0kam/ShutterClock/docs/measurements/data/2026-10-07_d7500_run2_timeline_100ms.csv

t_s | mean_A | max_A | vmin_V
0.0 | 0.00042 | 0.0022 | 8.9875
0.1 | 0.00044 | 0.0019 | 8.9857
0.2 | 0.00042 | 0.0018 | 8.9838
0.3 | 0.00049 | 0.0020 | 8.9875
0.4 | 0.00044 | 0.0026 | 8.9875
0.5 | 0.00042 | 0.0019 | 8.9838
0.6 | 0.00043 | 0.0018 | 8.9885
0.7 | 0.00044 | 0.0022 | 8.9838
0.8 | 0.00039 | 0.0022 | 8.9818
0.9 | 0.00044 | 0.0020 | 8.9857
1.0 | 0.00046 | 0.0019 | 8.9848
1.1 | 0.00043 | 0.0019 | 8.9875
1.2 | 0.00045 | 0.0021 | 8.9875
1.3 | 0.00044 | 0.0021 | 8.9848
1.4 | 0.00049 | 0.0019 | 8.9875
1.5 | 0.00046 | 0.0021 | 8.9857
1.6 | 0.00048 | 0.0022 | 8.9848
1.7 | 0.00044 | 0.0024 | 8.9895
1.8 | 0.00046 | 0.0018 | 8.9875
1.9 | 0.00042 | 0.0021 | 8.9857
2.0 | 0.00043 | 0.0019 | 8.9885
2.1 | 0.00046 | 0.0023 | 8.9875
2.2 | 0.00044 | 0.0022 | 8.9828
2.3 | 0.00042 | 0.0021 | 8.9838
2.4 | 0.00045 | 0.0019 | 8.9857
2.5 | 0.00048 | 0.0021 | 8.9865
2.6 | 0.00044 | 0.0020 | 8.9838
2.7 | 0.00046 | 0.0020 | 8.9865
2.8 | 0.00049 | 0.0021 | 8.9865
2.9 | 0.00044 | 0.0026 | 8.9875
3.0 | 0.00043 | 0.0016 | 8.9857
3.1 | 0.00043 | 0.0021 | 8.9857
3.2 | 0.00047 | 0.0020 | 8.9865
3.3 | 0.00044 | 0.0030 | 8.9885
3.4 | 0.00040 | 0.0020 | 8.9828
3.5 | 0.00051 | 0.0026 | 8.9885
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
