0kam/ShutterClock/docs/measurements/data/2026-10-07_d7500_run4_mf_shot_3200Hz.csv

t_s | vbus_V | current_A
47.50026 | 8.9961 | 0.000593
47.50057 | 9.0018 | 0.000593
47.50088 | 8.9979 | 0.000697
47.50119 | 8.9932 | 0.001089
47.50145 | 9.0035 | 0.001089
47.50176 | 9.0008 | -0.000111
47.50207 | 8.9941 | 0.001089
47.50238 | 8.9988 | 0.000881
47.50268 | 8.9988 | 0.000089
47.50300 | 8.9932 | 0.000697
47.50325 | 8.9961 | 0.000697
47.50356 | 8.9971 | 0.000193
47.50387 | 8.9971 | 0.000697
47.50418 | 8.9971 | -0.000111
47.50449 | 8.9998 | 0.000985
47.50474 | 8.9914 | 0.000985
47.50505 | 8.9941 | 0.000089
47.50536 | 8.9922 | 0.001089
47.50567 | 8.9941 | -0.000007
47.50598 | 9.0027 | -0.000111
47.50629 | 8.9951 | 0.000089
47.50654 | 8.9988 | 0.000089
47.50685 | 8.9979 | 0.000881
47.50716 | 8.9961 | -0.000111
47.50747 | 8.9971 | 0.000089
47.50778 | 8.9932 | 0.000697
47.50990 | 8.9971 | -0.000007
47.51166 | 9.0084 | 0.000593
47.51342 | 8.9979 | 0.000297
47.51518 | 9.0018 | 0.001489
47.51694 | 8.9988 | 0.000193
47.51869 | 9.0055 | 0.000489
47.52045 | 8.9922 | 0.000777
47.52221 | 8.9951 | 0.001673
47.52246 | 9.0027 | 0.001489
47.52277 | 9.0018 | 0.000489
47.52308 | 8.9961 | -0.000591
47.52339 | 8.9971 | 0.000297
47.52364 | 8.9961 | 0.000297
47.52395 | 9.0018 | 0.000985
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
