0kam/ShutterClock/docs/measurements/data/2026-10-07_d7500_run4_powerup_shot_3200Hz.csv

t_s | vbus_V | current_A
182.00012 | 0.0000 | -0.000591
182.00043 | 0.0000 | -0.000111
182.00073 | 0.0000 | -0.000511
182.00104 | 0.0000 | -0.000007
182.00130 | 0.0000 | -0.000007
182.00161 | 0.0000 | 0.000089
182.00192 | 0.0000 | -0.000111
182.00223 | 0.0000 | 0.000489
182.00254 | 0.0000 | 0.000777
182.00279 | 0.0000 | 0.000777
182.00310 | 0.0000 | 0.000297
182.00341 | 0.0000 | -0.000007
182.00372 | 0.0000 | -0.000111
182.00403 | 0.0000 | 0.000489
182.00434 | 0.0000 | -0.000591
182.00459 | 0.0000 | -0.000591
182.00490 | 0.0000 | 0.000593
182.00521 | 0.0000 | 0.000193
182.00552 | 0.0000 | -0.000399
182.00583 | 0.0000 | 0.000193
182.00614 | 0.0000 | 0.000385
182.00639 | 0.0000 | 0.000385
182.00670 | 0.0000 | 0.000089
182.00701 | 0.0000 | 0.000777
182.00732 | 0.0000 | 0.000297
182.00763 | 0.0000 | -0.000295
182.00794 | 0.0000 | -0.000903
182.00820 | 0.0000 | -0.000903
182.00851 | 0.0000 | -0.000191
182.00882 | 0.0002 | -0.000007
182.00913 | 0.0000 | 0.001089
182.00944 | 0.0000 | 0.000089
182.00969 | 0.0000 | 0.000089
182.01000 | 0.0000 | -0.000295
182.01031 | 0.0000 | 0.000489
182.01062 | 0.0000 | 0.000985
182.01093 | 0.0000 | 0.000089
182.01124 | 0.0000 | 0.000089
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
